MATE-Leviathan/dory/firmware/main/board/buzzer.h

#pragma once

#include <stdbool.h>

void buzzer_init(void);
void buzzer_tone(int hz);
void buzzer_off(void);
void buzzer_play_samsung_boot(void);
void buzzer_play_starting_beeps(void);
void buzzer_start_leak_alarm(void);
void buzzer_stop_leak_alarm(void);
bool buzzer_leak_alarm_is_on(void);
