MATE-Leviathan/dory/firmware/main/board/battery.c

#include "battery.h"

#include "esp_adc/adc_cali.h"
#include "esp_adc/adc_cali_scheme.h"
#include "esp_adc/adc_oneshot.h"
#include "esp_err.h"
#include "esp_log.h"

#include "board_pins.h"

static const char *TAG = "battery";

static adc_oneshot_unit_handle_t adc_handle;
static adc_cali_handle_t adc_cali_handle;

void battery_init(void)
{
    adc_oneshot_unit_init_cfg_t unit_cfg = {
        .unit_id = ADC_UNIT_1,
    };
    ESP_ERROR_CHECK(adc_oneshot_new_unit(&unit_cfg, &adc_handle));

    adc_oneshot_chan_cfg_t chan_cfg = {
        .atten = ADC_ATTEN_DB_12,
        .bitwidth = ADC_BITWIDTH_12,
    };
    ESP_ERROR_CHECK(adc_oneshot_config_channel(adc_handle, BATT_ADC_CHANNEL, &chan_cfg));

    adc_cali_curve_fitting_config_t cali_cfg = {
        .unit_id = ADC_UNIT_1,
        .chan = BATT_ADC_CHANNEL,
        .atten = ADC_ATTEN_DB_12,
        .bitwidth = ADC_BITWIDTH_12,
    };
    ESP_ERROR_CHECK(adc_cali_create_scheme_curve_fitting(&cali_cfg, &adc_cali_handle));
    ESP_LOGI(TAG, "Battery ADC initialized");
}

float battery_voltage_read(void)
{
    int raw = 0;
    int mv = 0;
    float voltage;

    ESP_ERROR_CHECK(adc_oneshot_read(adc_handle, BATT_ADC_CHANNEL, &raw));

    ESP_ERROR_CHECK(adc_cali_raw_to_voltage(adc_cali_handle, raw, &mv));

    voltage = (mv / 1000.0f) * BATT_DIVIDER_MULTIPLIER;
    ESP_LOGI(TAG, "Battery voltage: %.2f V", voltage);
    return voltage;
}
